svenpetersen1965/C64-A-V-Adaptor/case/Rev. 0/inkscape/AV_5pin_label.png

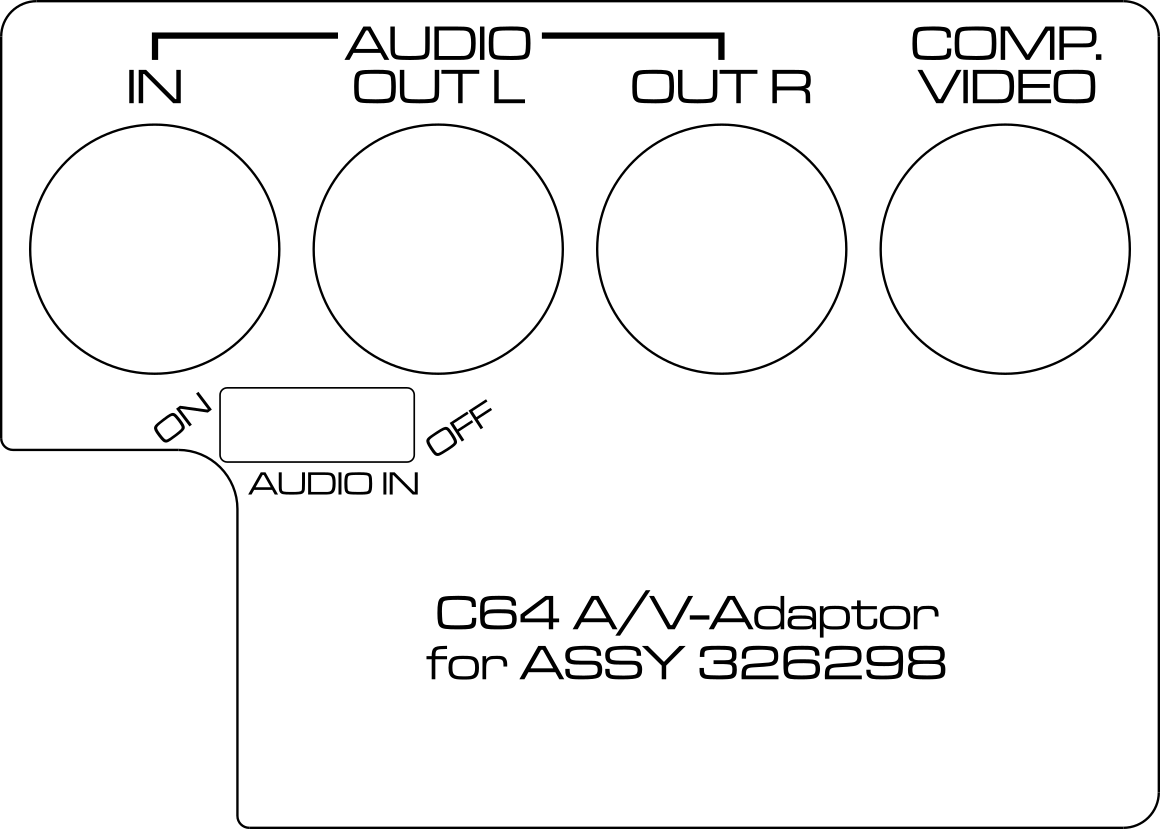
case/Rev. 0/inkscape/AV_5pin_label.png
