svenpetersen1965/C64-A-V-Adaptor/case/Rev. 0/inkscape/AV_7pin_label.png

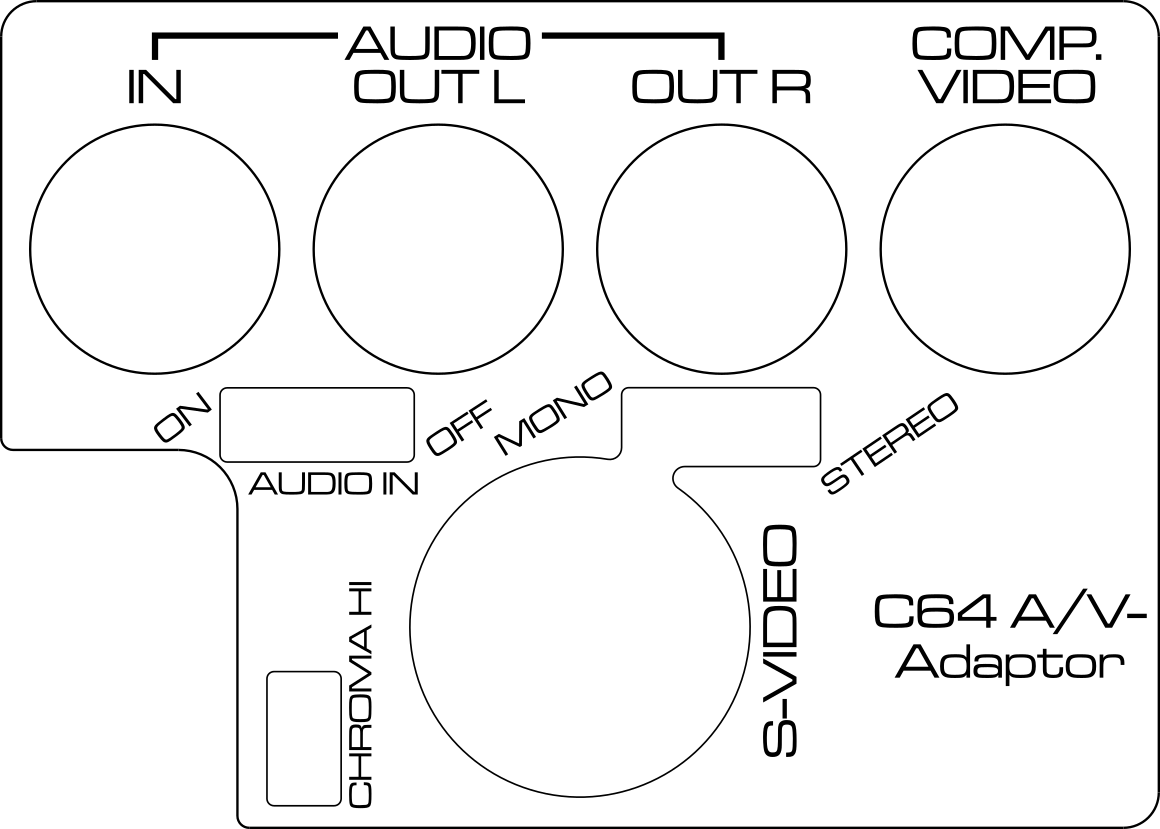
case/Rev. 0/inkscape/AV_7pin_label.png
