svenpetersen1965/C64-A-V-Adaptor/case/Rev. 0/pictures/2866_-_adaptor with C64C.JPG

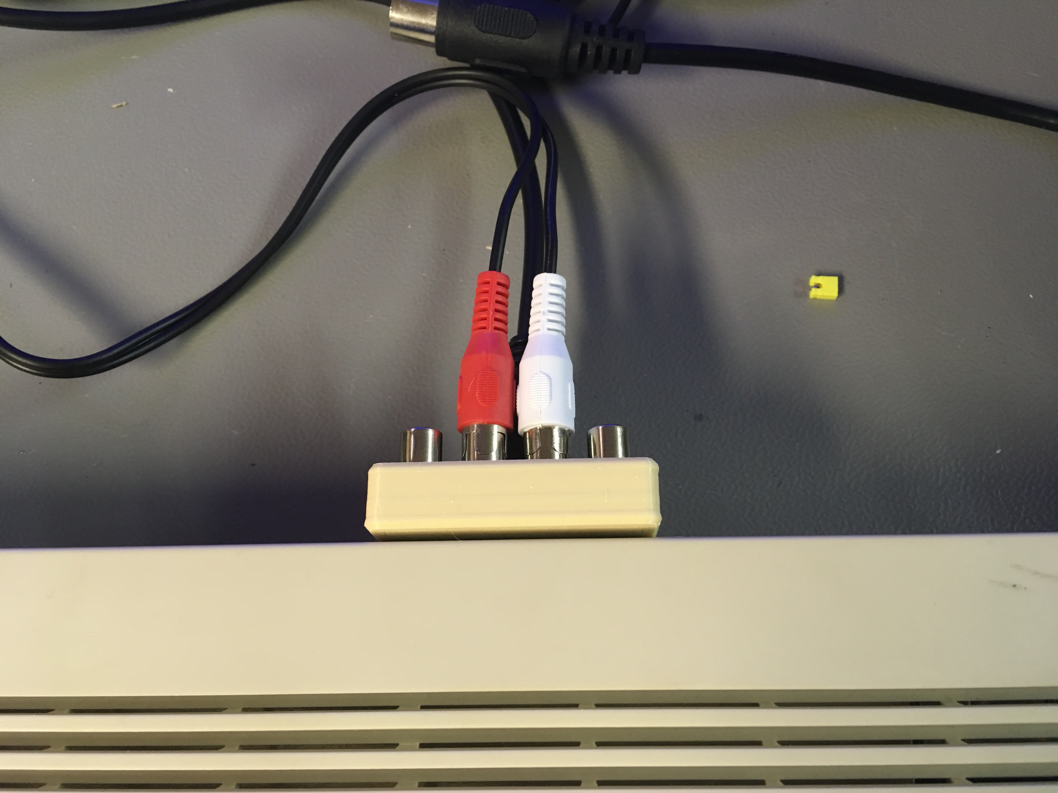
case/Rev. 0/pictures/2866_-_adaptor with C64C.JPG
