svenpetersen1965/C64-A-V-Adaptor/case/Rev. 0/pictures/AV-Adaptor_case_5pin v5.png

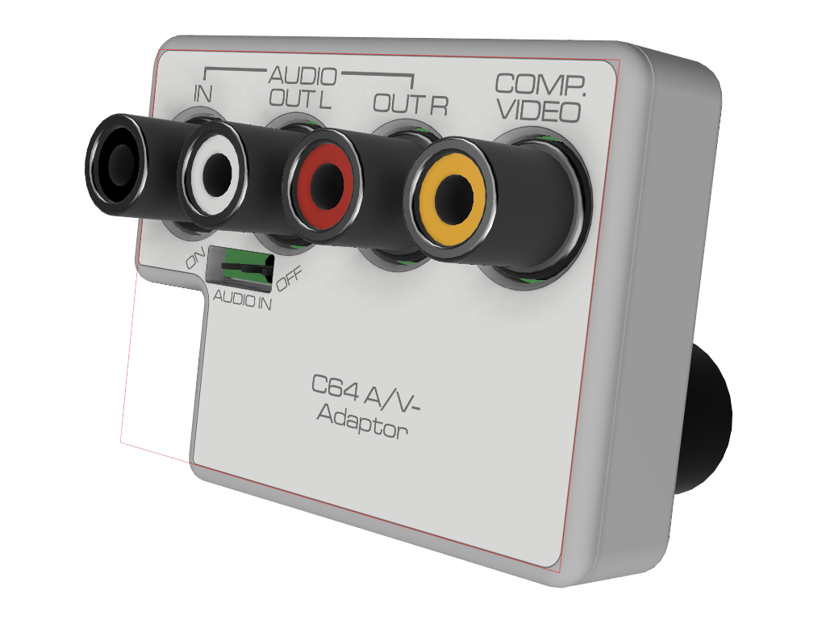
case/Rev. 0/pictures/AV-Adaptor_case_5pin v5.png
