svenpetersen1965/C64-A-V-Adaptor/case/Rev. 0/pictures/AV-Adaptor_case_open.png

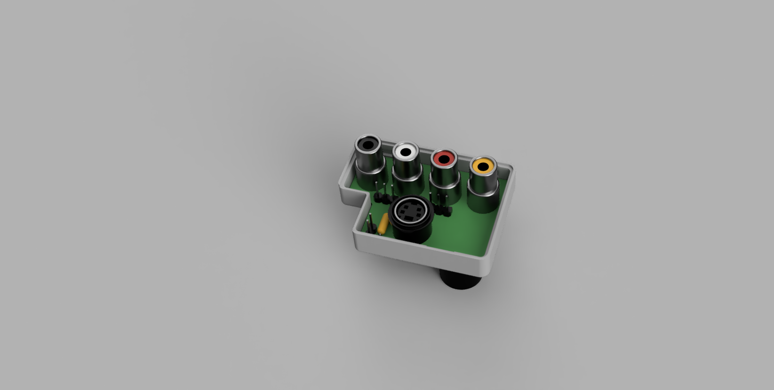
case/Rev. 0/pictures/AV-Adaptor_case_open.png
