svenpetersen1965/C64-A-V-Adaptor/case/Rev. 0/pictures/AV-Adaptor_case_VIC-20 v6.png

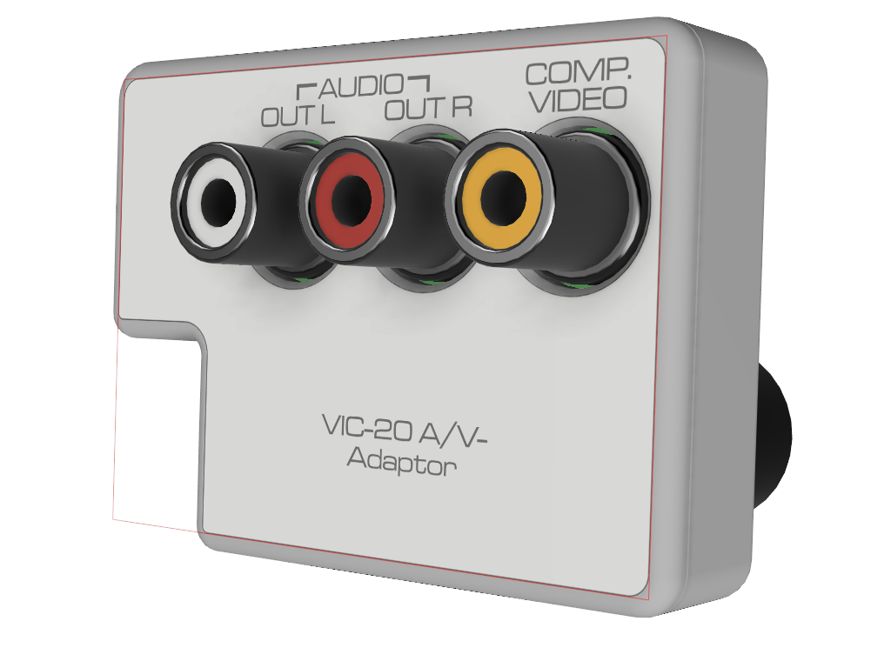
case/Rev. 0/pictures/AV-Adaptor_case_VIC-20 v6.png
