svenpetersen1965/C64-A-V-Adaptor/case/Rev. 0/pictures/Label_VIC-20.png

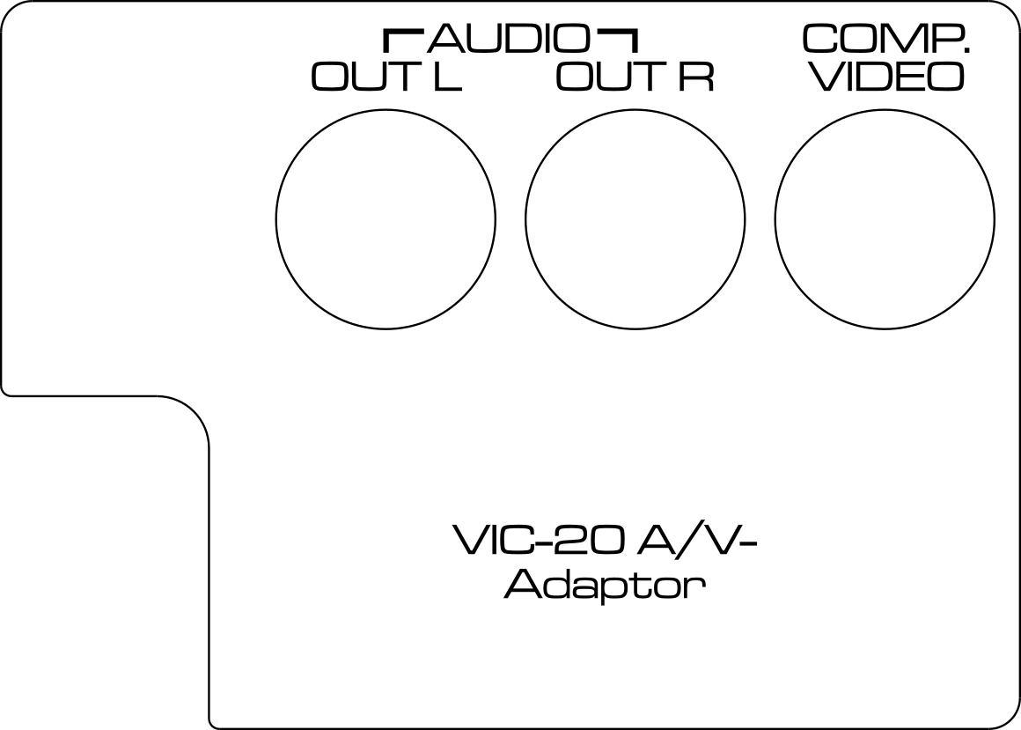
case/Rev. 0/pictures/Label_VIC-20.png
