svenpetersen1965/C64-A-V-Adaptor/Rev. 2/pictures/10pcs-lot-4-Pin-Mini-DIN-Female-Socket-Connector-4Pin-DIN-Mini-Jack-PS2-Mini-Circular.jpg

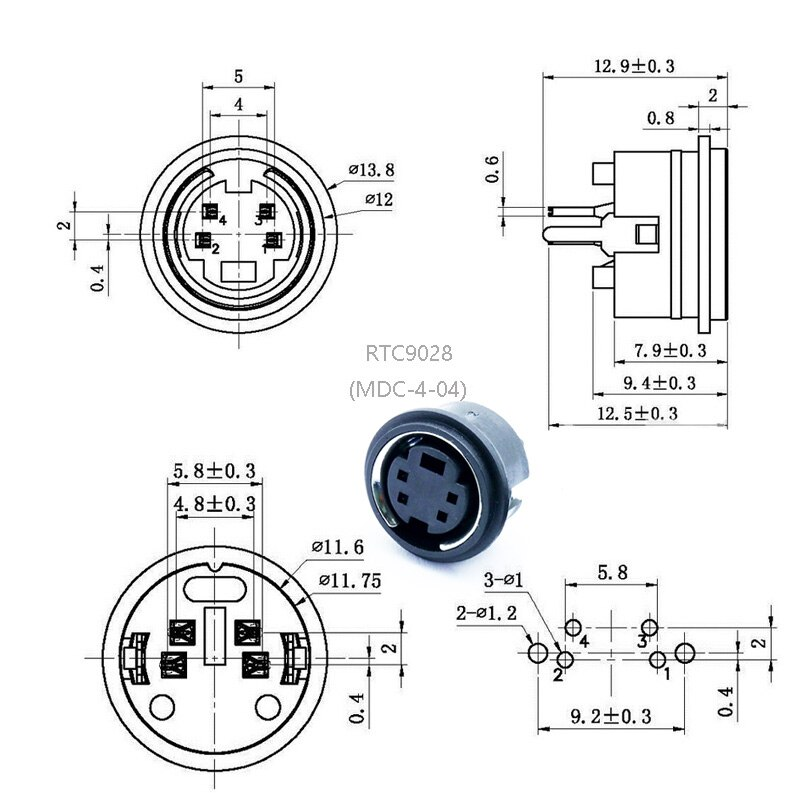
Rev. 2/pictures/10pcs-lot-4-Pin-Mini-DIN-Female-Socket-Connector-4Pin-DIN-Mini-Jack-PS2-Mini-Circular.jpg
