svenpetersen1965/C64-A-V-Adaptor/Rev. 2/pictures/2140_-_AV_Ada_V2_top.JPG

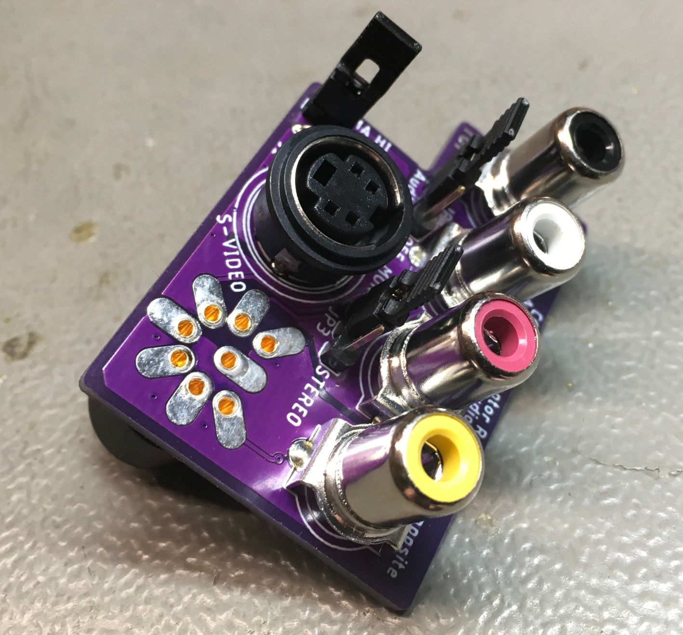
Rev. 2/pictures/2140_-_AV_Ada_V2_top.JPG
