svenpetersen1965/C64-A-V-Adaptor/Rev. 2/pictures/2141_-_AV_Ada_V2_bottom.JPG

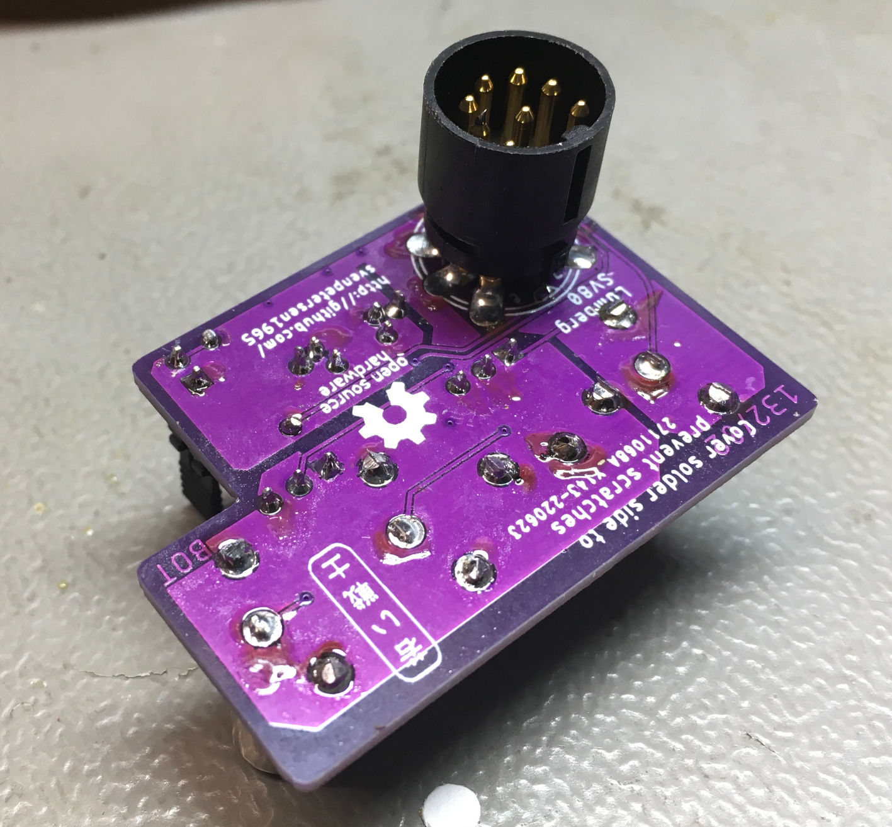
Rev. 2/pictures/2141_-_AV_Ada_V2_bottom.JPG
