svenpetersen1965/C64-A-V-Adaptor/Rev. 2/pictures/C64_AV-Adaptor_bot.png

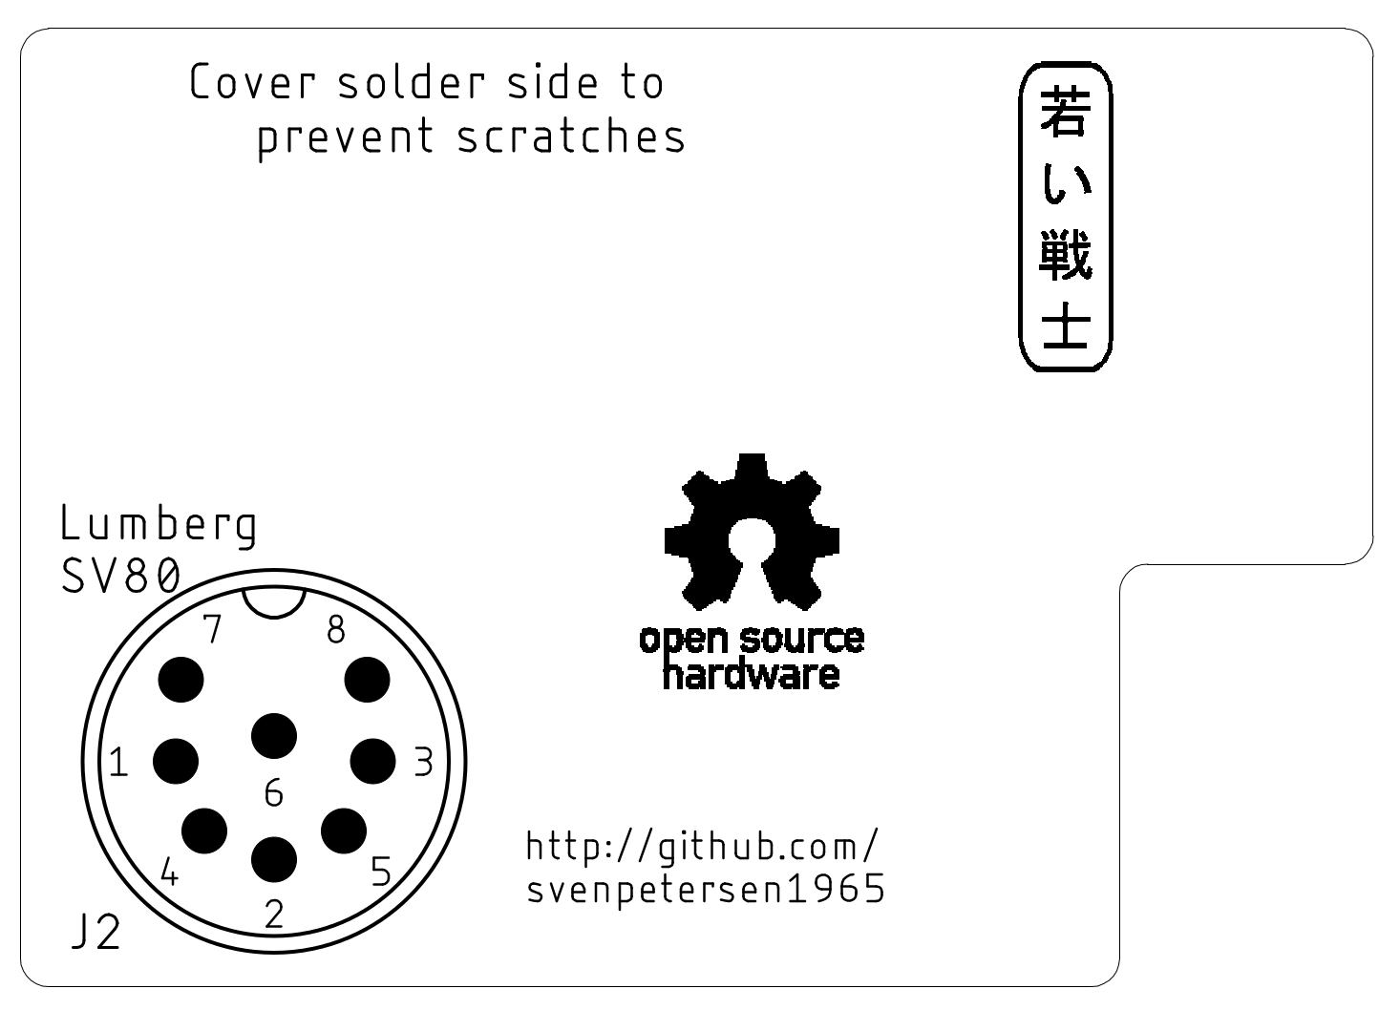
Rev. 2/pictures/C64_AV-Adaptor_bot.png
